aawilliams85/ViveTrackerInterfaceBoard/Images/Original_Board_Bottom.jpg

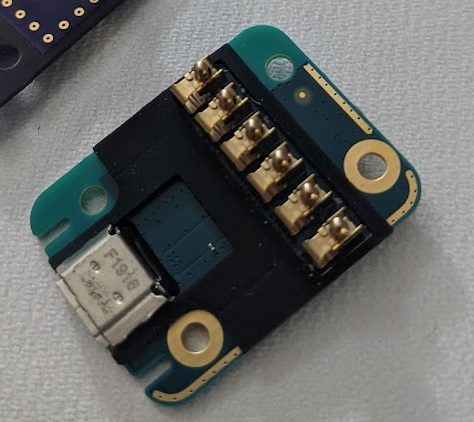
Images/Original_Board_Bottom.jpg
